N8WM/raspi-play/images/IMG_8660.jpeg

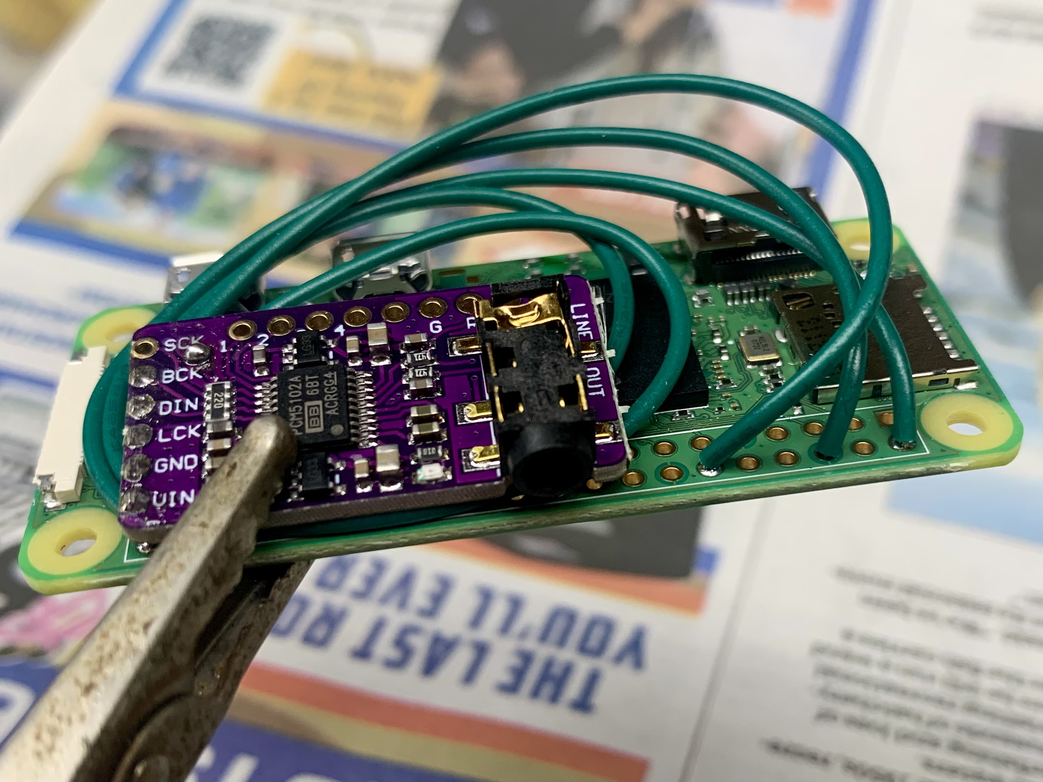
images/IMG_8660.jpeg
