N8WM/raspi-play/images/IMG_8680.jpeg

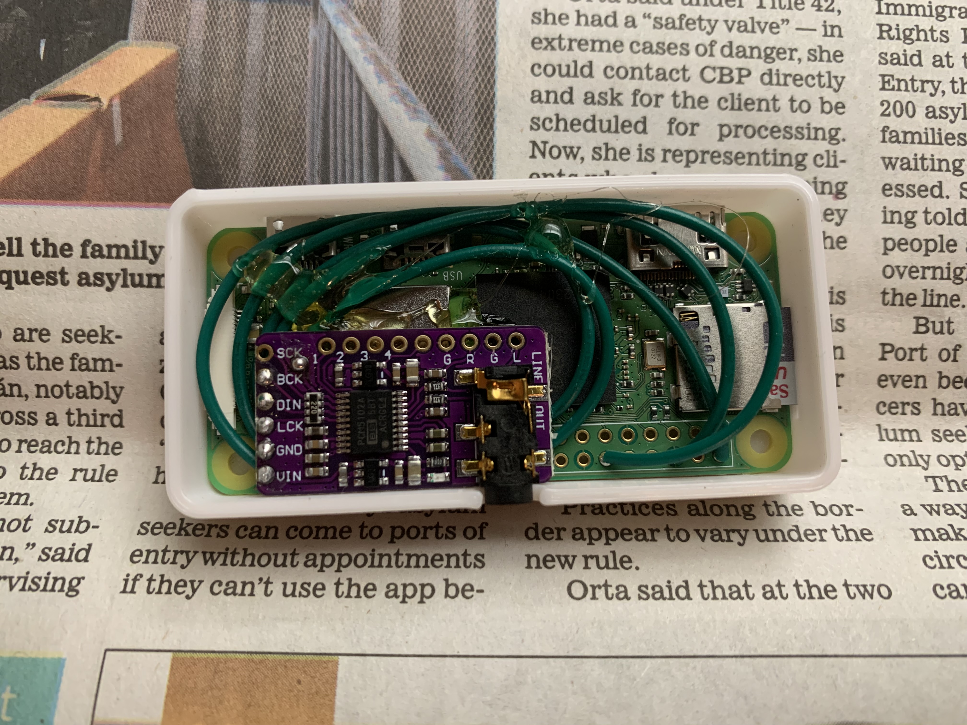
images/IMG_8680.jpeg
